LabDig/SoilSmartSensor/App/PrintScrenn/Screenshot_20230918_122818.jpg

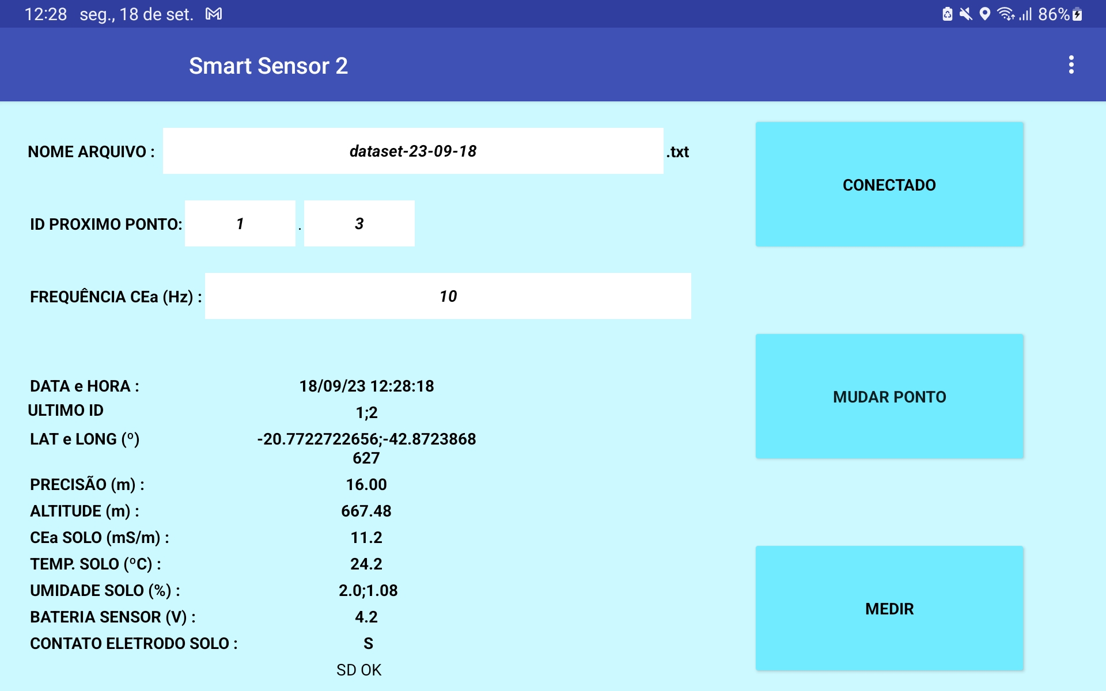
App/PrintScrenn/Screenshot_20230918_122818.jpg
